joe-jordan/scad_woodwork/mft_assets/Workbench_full_below.png

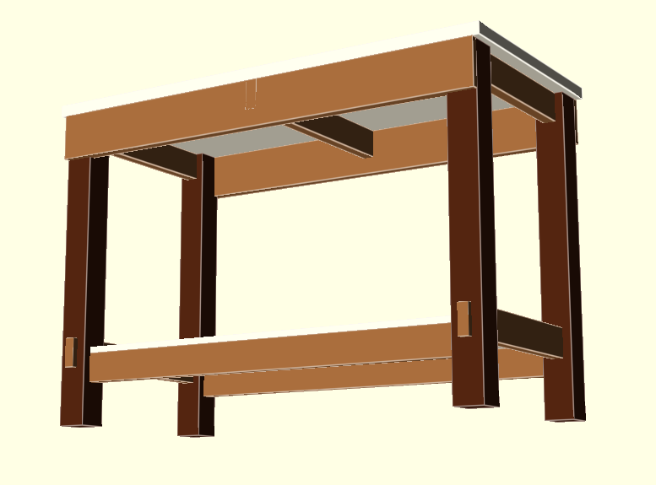
mft_assets/Workbench_full_below.png
