joe-jordan/scad_woodwork/screenshots/workbench_trestles_bottom.png

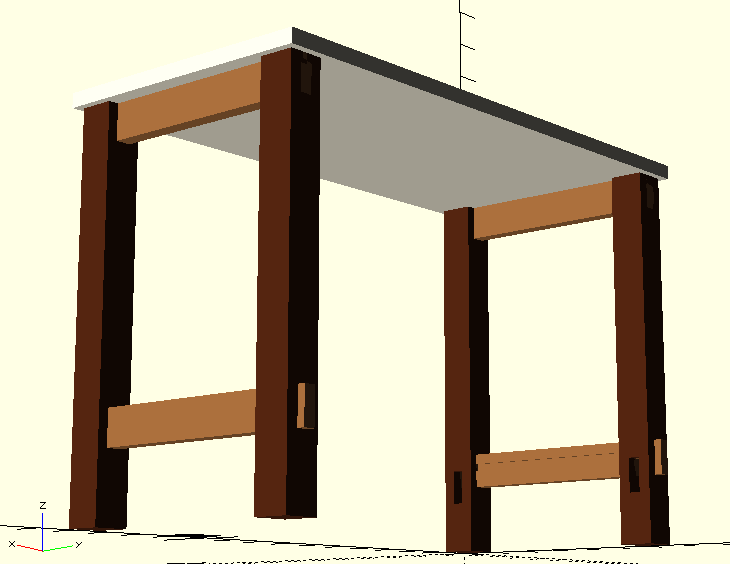
screenshots/workbench_trestles_bottom.png
