joe-jordan/scad_woodwork/screenshots/worktop_v1_back.png

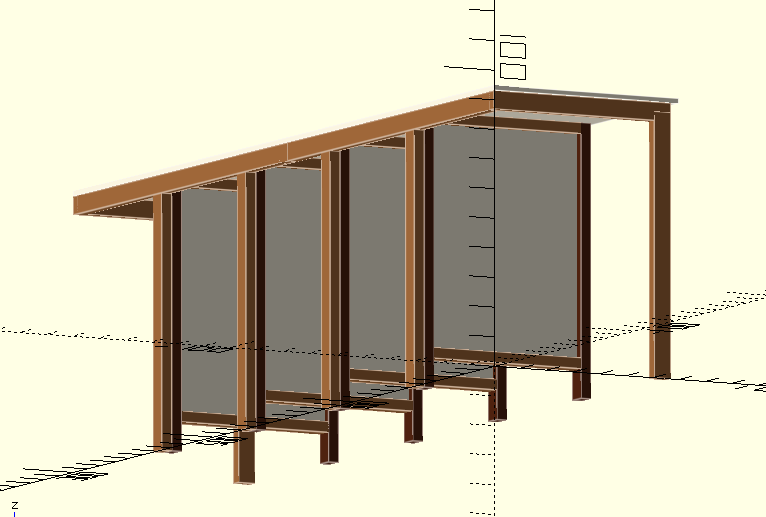
screenshots/worktop_v1_back.png
