joe-jordan/scad_woodwork/screenshots/worktop_v1_top.png

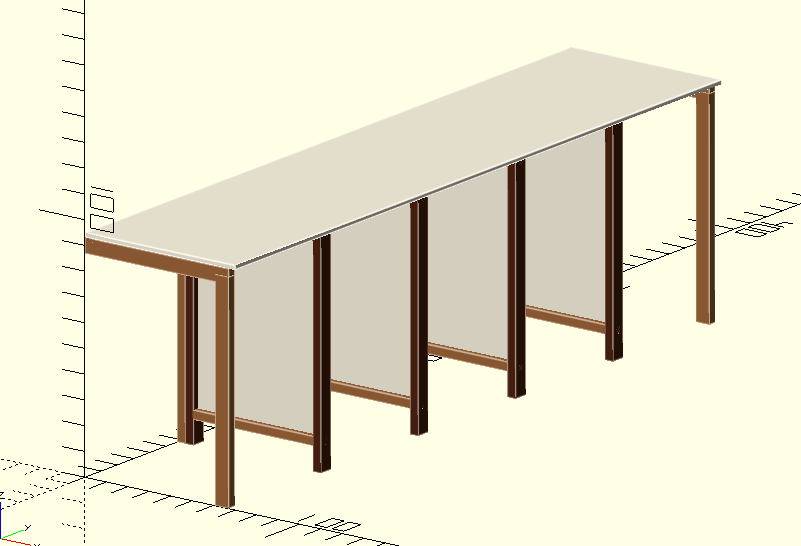
screenshots/worktop_v1_top.png
