joe-jordan/scad_woodwork/workbench/lumber_dimensions.scad

// for differences:
delta = 0.1;

// lumber dimensions
ply_thickness = 1.8;
two_by = 3.8;
four_by = 8.9;
six_by = 14;
