joe-jordan/scad_woodwork/worktop/lumber_dimensions.scad

// for differences:
delta = 0.1;

// lumber dimensions
ply_thickness_top = 1.8;
ply_thickness_panel = 1.2;
// CLS studs (2x3, really)
two_by = 3.8;
four_by = 6.3;
three_by = 6.3; // TODO fix all refs to this in worktop.
